JacksonSchreiber/sticks3-run-display/docs/images/sleeve-v8-front-compare.png

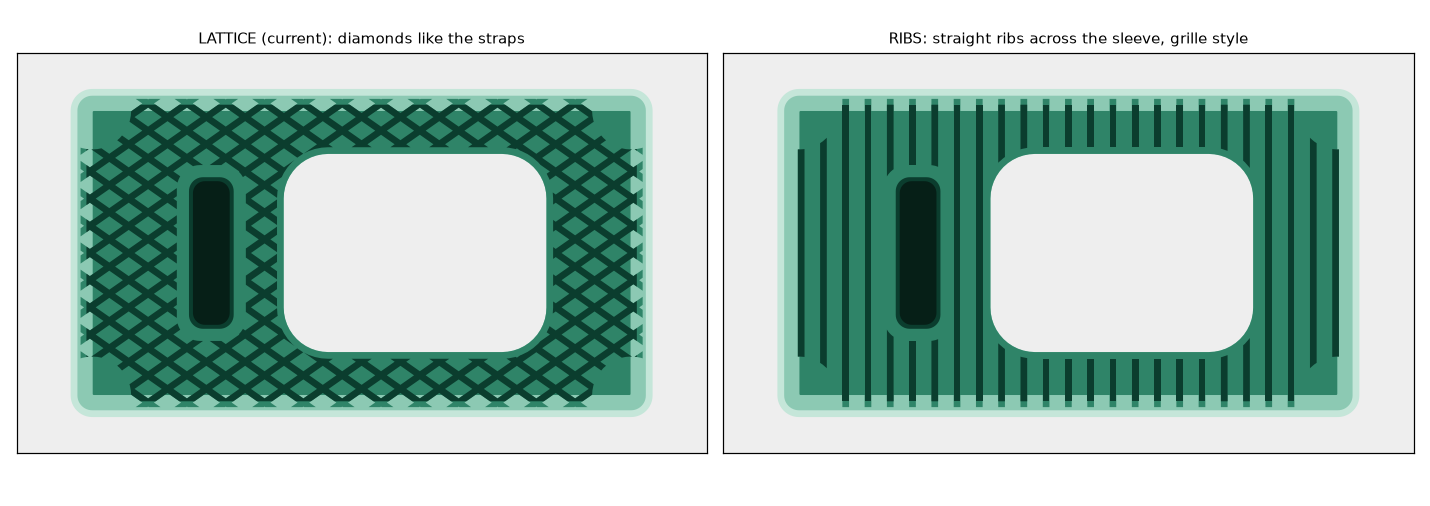
docs/images/sleeve-v8-front-compare.png
