JacksonSchreiber/sticks3-run-display/docs/images/sleeve-v8-knurl-compare.png

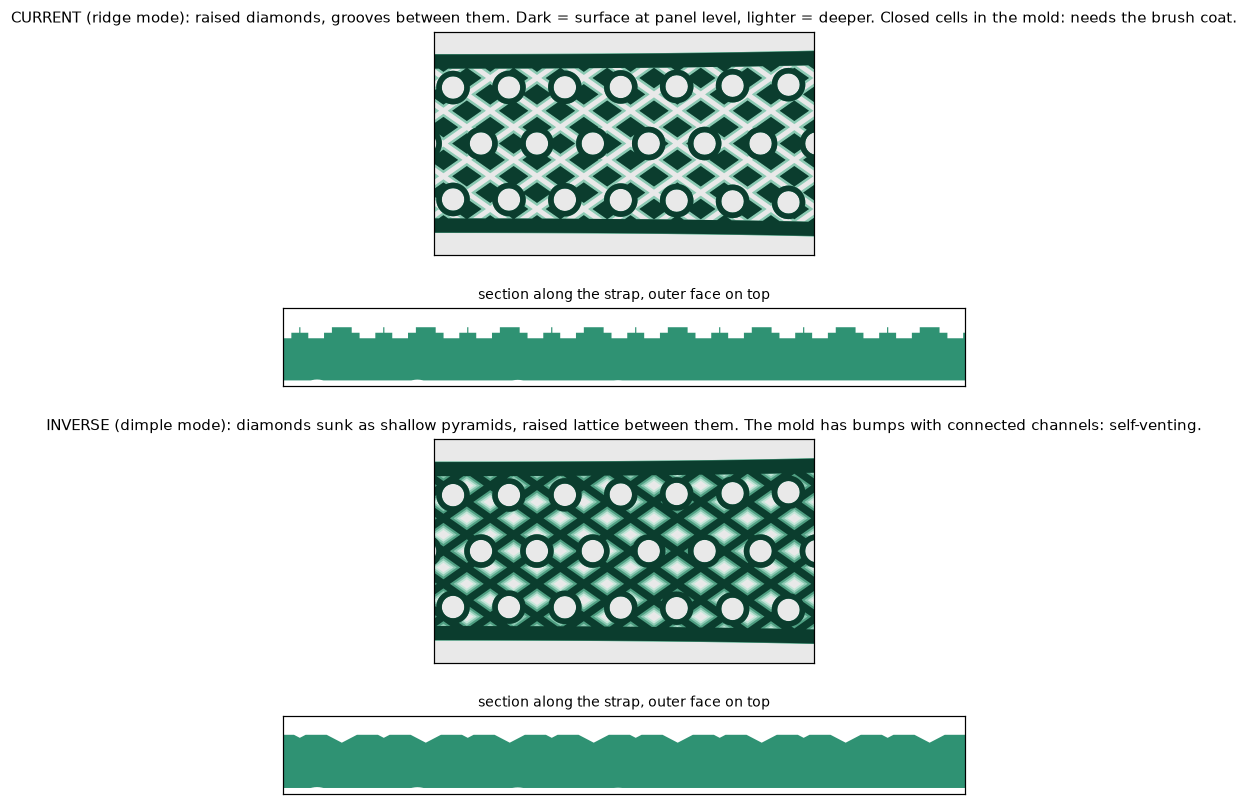
docs/images/sleeve-v8-knurl-compare.png
