JacksonSchreiber/sticks3-run-display/hardware/sleeve/print/sleeve_core_upper_lower.3mf

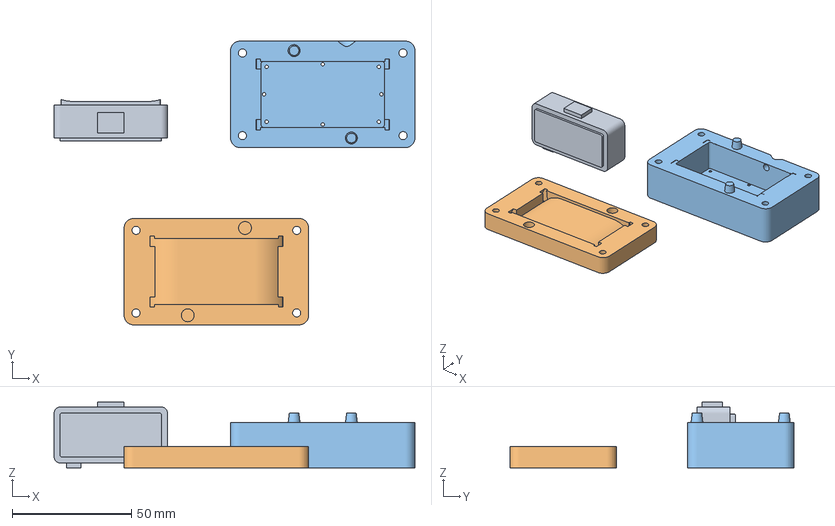
[picture p23: CAD file, 2026-09-24, an earlier design]
hardware/sleeve/print/sleeve_core_upper_lower.3mf
151.2 x 118.9 x 27.6 mm
sleeve_core.stl
sleeve_mold_bottom.stl
sleeve_mold_top.stl
