JacksonSchreiber/sticks3-run-display/hardware/sleeve/stl/sleeve_preview_not_for_printing.stl

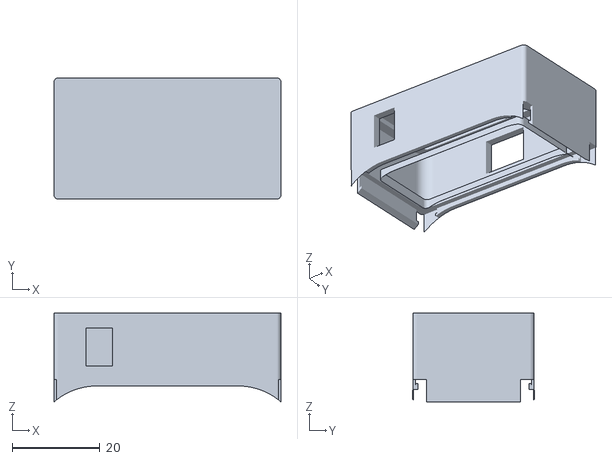
[picture p24: CAD file, 2026-09-24, an earlier design]
hardware/sleeve/stl/sleeve_preview_not_for_printing.stl
51.6 x 27.6 x 20.2
