JacksonSchreiber/sticks3-run-display/hardware/sleeve_v2/print/sleeve_staple_x2.3mf

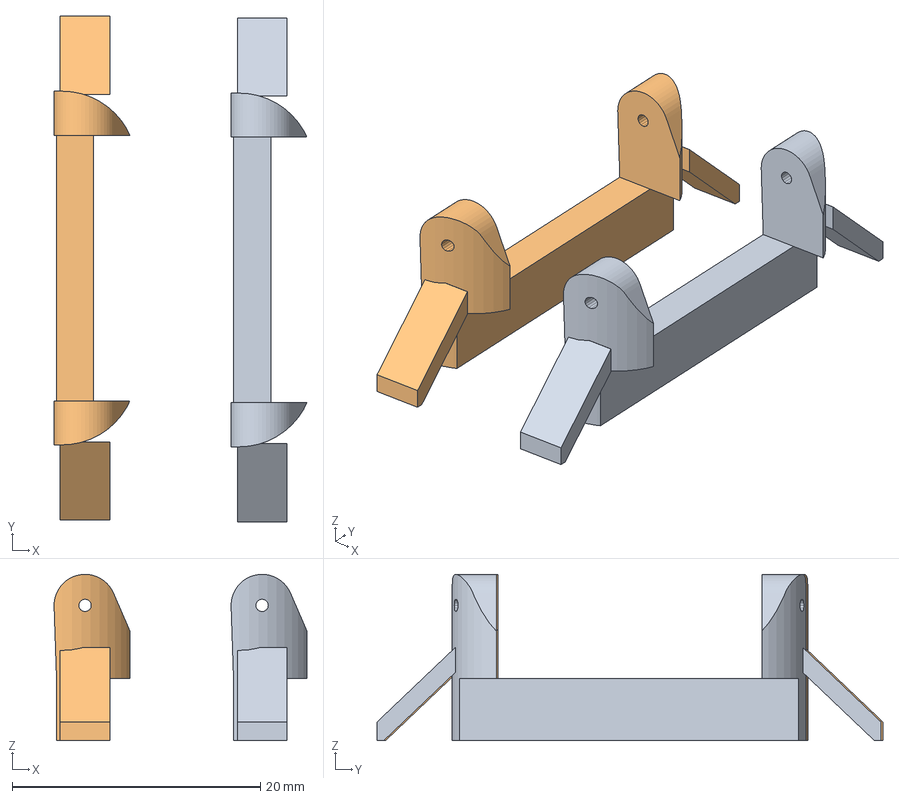
[picture p25: CAD file, 2026-09-24, an earlier design]
hardware/sleeve_v2/print/sleeve_staple_x2.3mf
20.4 x 40.8 x 13.4 mm
sleeve_staple.stl x 2
